unborlex/vfd/20250319_105156.jpg

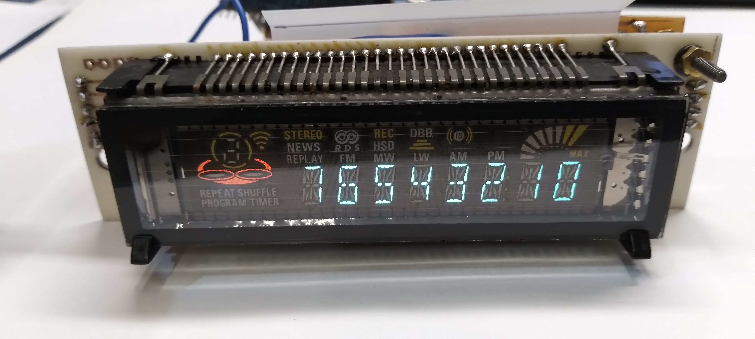
20250319_105156.jpg
