unborlex/vfd/20250319_105201.jpg

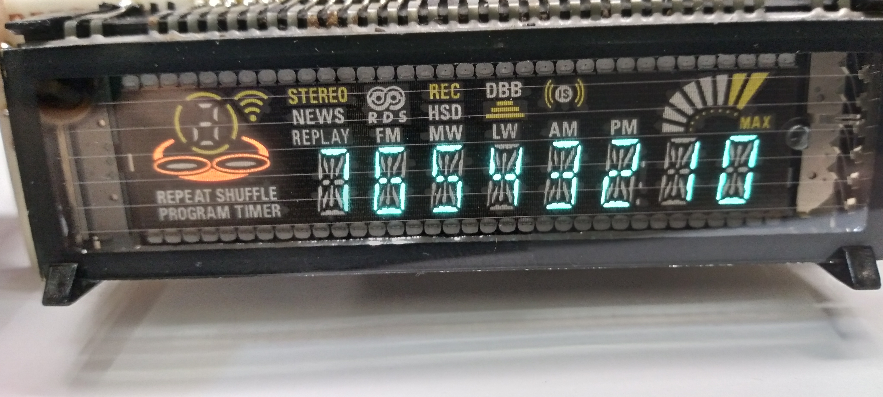
20250319_105201.jpg
