unborlex/vfd/20250319_105211.jpg

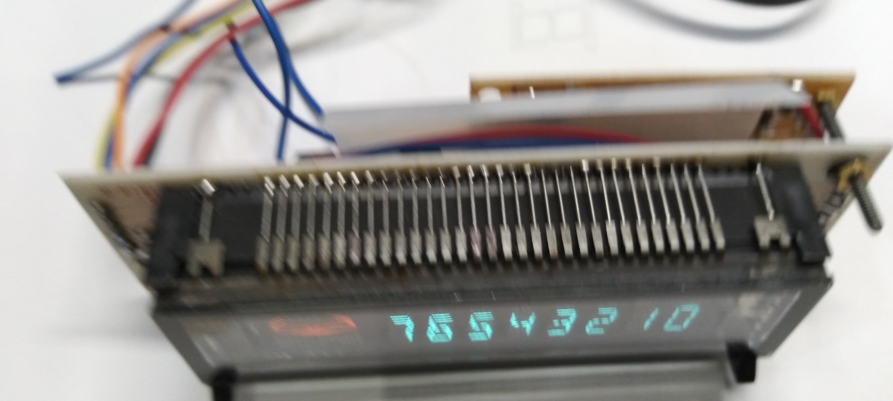
20250319_105211.jpg
