unborlex/vfd/20250319_105217.jpg

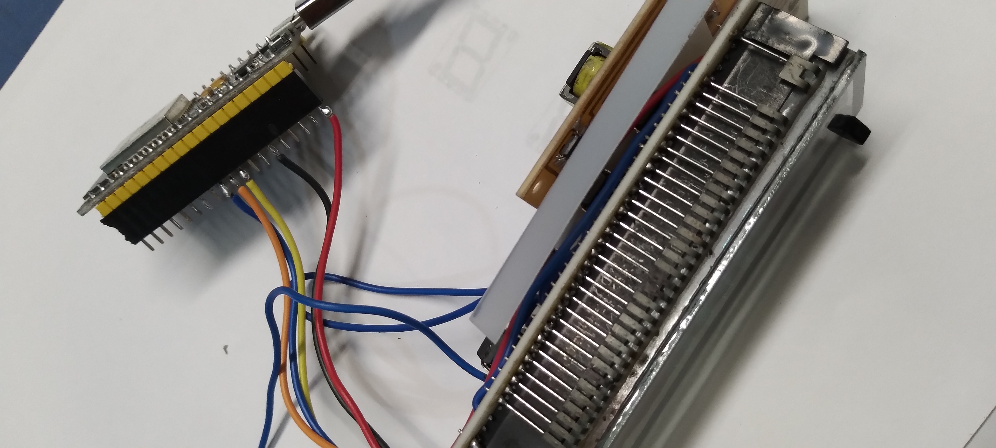
20250319_105217.jpg
