unborlex/vfd/20250319_105233.jpg

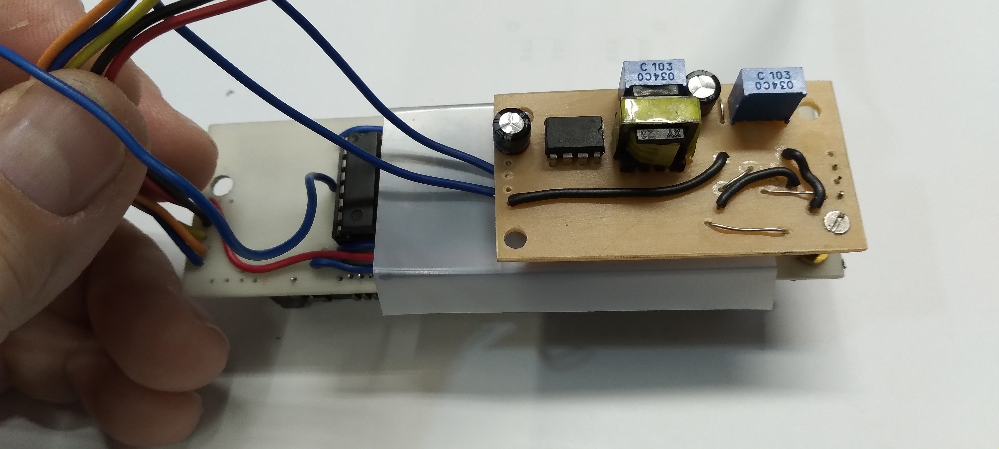
20250319_105233.jpg
