unborlex/vfd/20250319_105242.jpg

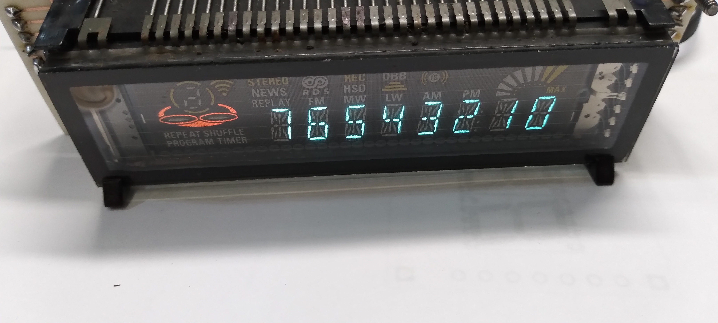
20250319_105242.jpg
