unborlex/vfd/20250319_105323.jpg

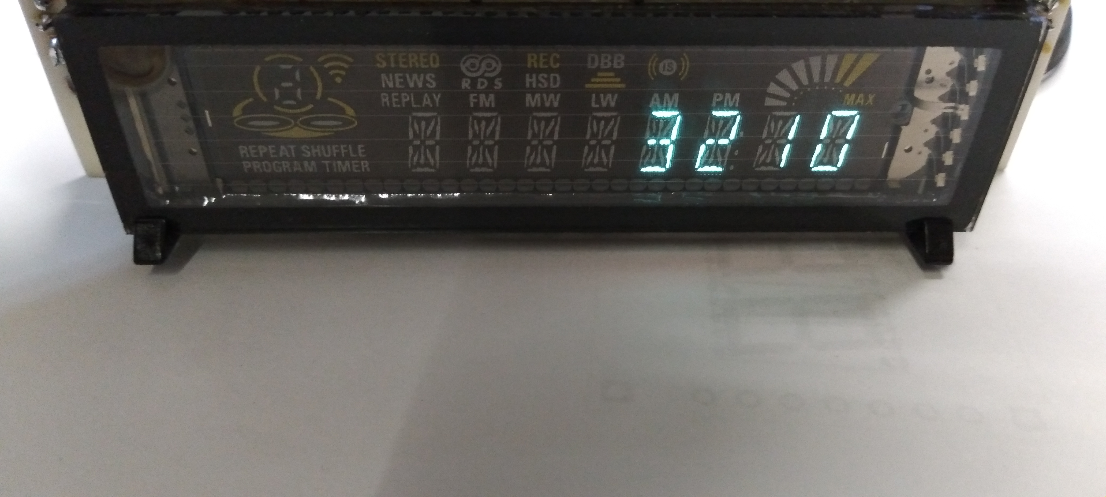
20250319_105323.jpg
