unborlex/vfd/VDF_2025.sch

## EAGLE design VDF_2025.sch (2025-03-19)

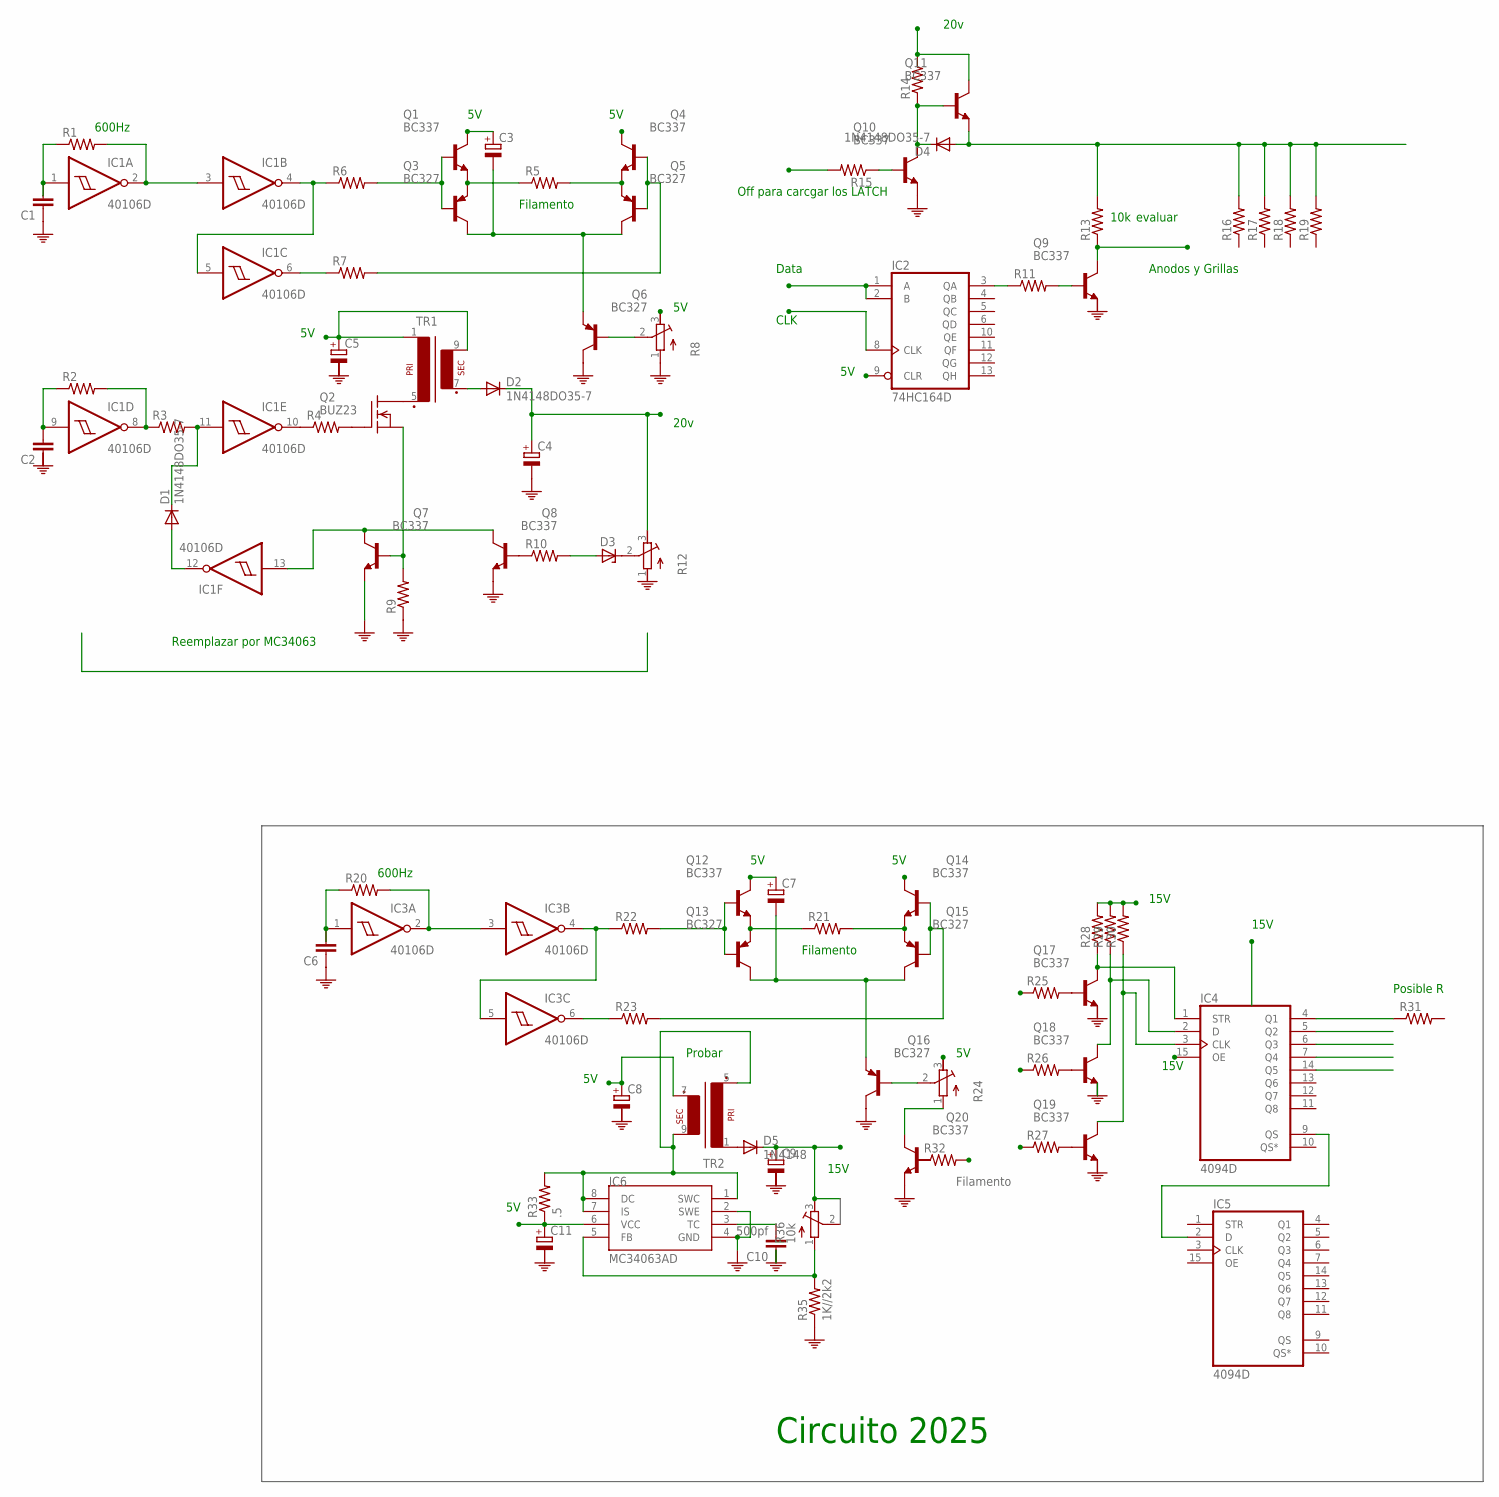
[picture p12: schematic VDF_2025.sch]

Parts:
C1, C2, C6: C-EU025-060X050; C025-060X050
C3, C4, C5, C7, C8, C9, C11: CPOL-EU139CLL-2R; 139CLL-2R
C10: 500pf; C025-060X050
D1, D2, D4: 1N4148DO35-7; DO35-7
D3: ZENER-DIODEDO13M; DO13M
D5: 1N4148; DO35-7
IC1, IC3: 40106D; SO14
IC2: 74HC164D; SO14
IC4, IC5: 4094D; SO16
IC6: MC34063AD; SOIC8
Q1, Q4, Q7, Q8, Q9, Q10, Q11, Q12, Q14, Q17, Q18, Q19, Q20: BC337; TO92
Q2: BUZ23; TO3
Q3, Q5, Q6, Q13, Q15, Q16: BC327; TO18
R1, R2, R3, R4, R5, R6, R7, R9, R10, R11, R13, R14, R15, R16, R17, R18, R19, R20, R21, R22, R23, R25, R26, R27, R28, R29, R30, R31, R32: R-US_0414/5V; 0414V
R8, R12, R24: R-TRIMM3103; RTRIM3103
R33: .5; 0414V
R35: 1K//2k2; 0414V
R36: 10k; RTRIM3103
TR1, TR2: EI42-1

Connections:
unnamed: IC1.8 (O), R2.2, R3.1
unnamed: D1.C, IC1.11 (I), R3.2
unnamed: IC1.10 (O), R4.1
unnamed: C5.+, TR1.1, TR1.9 (S4)
unnamed: C2.2, IC1.9 (I), R2.1
unnamed: Q2.2 (G), R4.2
unnamed: C3.-, Q3.3 (C), Q5.3 (C), Q6.1 (E)
unnamed: Q1.2 (B), Q3.2 (B), R6.2
unnamed: C3.+, Q1.3 (C)
unnamed: Q4.1 (E), Q5.1 (E), R5.2
unnamed: Q1.1 (E), Q3.1 (E), R5.1
unnamed: Q4.2 (B), Q5.2 (B), R7.2
unnamed: IC1.4 (O), IC1.5 (I), R6.1
unnamed: D2.A, TR1.7 (S3)
unnamed: IC1.6 (O), R7.1
unnamed: C4.+, D2.C, R12.3 (E)
unnamed: IC1.2 (O), IC1.3 (I), R1.2
unnamed: C1.2, IC1.1 (I), R1.1
unnamed: Q6.2 (B), R8.2 (S)
unnamed: IC1.13 (I), Q7.3 (C), Q8.3 (C)
unnamed: D1.A, IC1.12 (O)
unnamed: Q8.2 (B), R10.1
unnamed: Q2.1 (S), Q7.2 (B), R9.2
unnamed: D3.A, R10.2
unnamed: Q2.3 (D), TR1.5 (P2)
unnamed: D3.C, R12.2 (S)
unnamed: IC2.1 (A), IC2.2 (B)
unnamed: IC2.3 (QA), R11.1
unnamed: Q9.2 (B), R11.2
unnamed: Q9.3 (C), R13.1
unnamed: C7.+, Q12.3 (C)
unnamed: Q11.3 (C), R14.2
unnamed: D4.C, Q10.3 (C), Q11.2 (B), R14.1
unnamed: D4.A, Q11.1 (E), R13.2, R16.2, R17.2, R18.2, R19.2
unnamed: Q10.2 (B), R15.1
unnamed: Q14.1 (E), Q15.1 (E), R21.2
unnamed: Q12.1 (E), Q13.1 (E), R21.1
unnamed: C7.-, Q13.3 (C), Q15.3 (C), Q16.1 (E)
unnamed: Q12.2 (B), Q13.2 (B), R22.2
unnamed: Q14.2 (B), Q15.2 (B), R23.2
unnamed: IC3.4 (O), IC3.5 (I), R22.1
unnamed: IC3.6 (O), R23.1
unnamed: IC3.2 (O), IC3.3 (I), R20.2
unnamed: C6.2, IC3.1 (I), R20.1
unnamed: Q16.2 (B), R24.2 (S)
unnamed: C8.+, TR2.7 (S3)
unnamed: Q17.2 (B), R25.2
unnamed: Q18.2 (B), R26.2
unnamed: Q19.2 (B), R27.2
unnamed: IC4.1 (STR), Q17.3 (C), R28.1
unnamed: IC4.2 (D), Q18.3 (C), R29.1
unnamed: IC4.3 (CLK), Q19.3 (C), R30.1
unnamed: R28.2, R29.2, R30.2
unnamed: IC4.4 (Q1), R31.1
unnamed: IC4.9 (QS), IC5.2 (D)
unnamed: Q20.3 (C), R24.1 (A)
unnamed: IC6.1 (SWC), IC6.7 (IS), IC6.8 (DC), R33.2, TR2.5 (P2), TR2.9 (S4)
unnamed: C11.+, IC6.6 (VCC), R33.1
unnamed: D5.A, TR2.1
unnamed: C9.+, D5.C, R36.3 (E)
unnamed: C10.2, IC6.3 (TC)
unnamed: IC6.5 (FB), R35.2, R36.1 (A)
PE: C1.1, C4.-, C6.1, C10.1, IC6.2 (SWE), IC6.4 (GND), Q6.3 (C), Q8.1 (E), Q10.1 (E), Q16.3 (C), Q18.1 (E), Q20.1 (E), R8.1 (A), R9.1, R35.1

Notes on the sheet:
Filamento
600Hz
20v
Reemplazar por MC34063
CLK
Data
10k
evaluar
Off para carcgar los LATCH
Anodos y Grillas
15V
Circuito 2025
Posible R
Probar
